ableTI/pws/fotos/eindprod.png

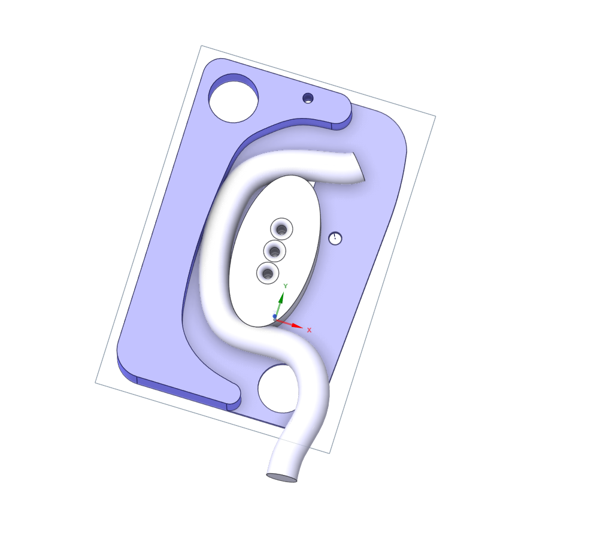
fotos/eindprod.png
