ableTI/pws/fotos/schets_snelheid_ontw.jpg

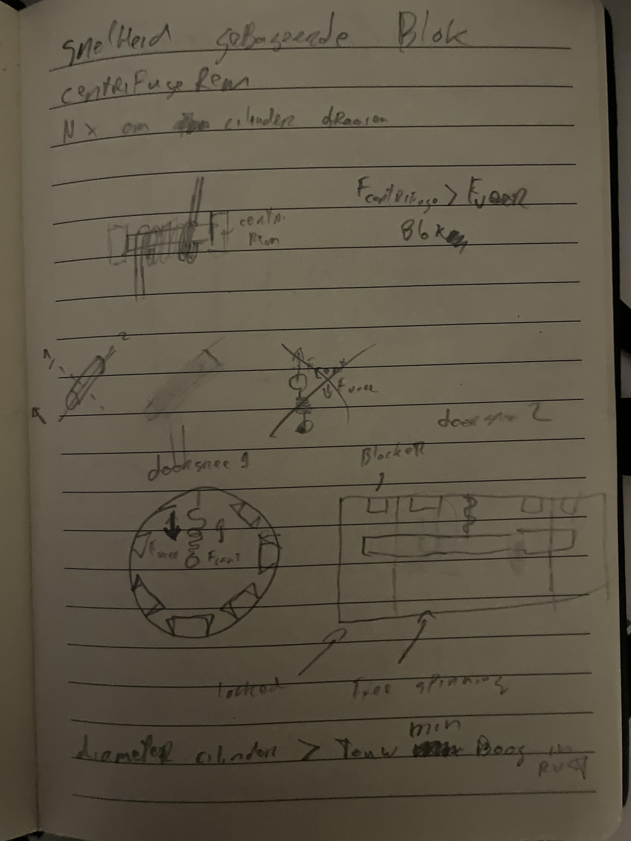
fotos/schets_snelheid_ontw.jpg
