ableTI/pws/fotos/v6.png

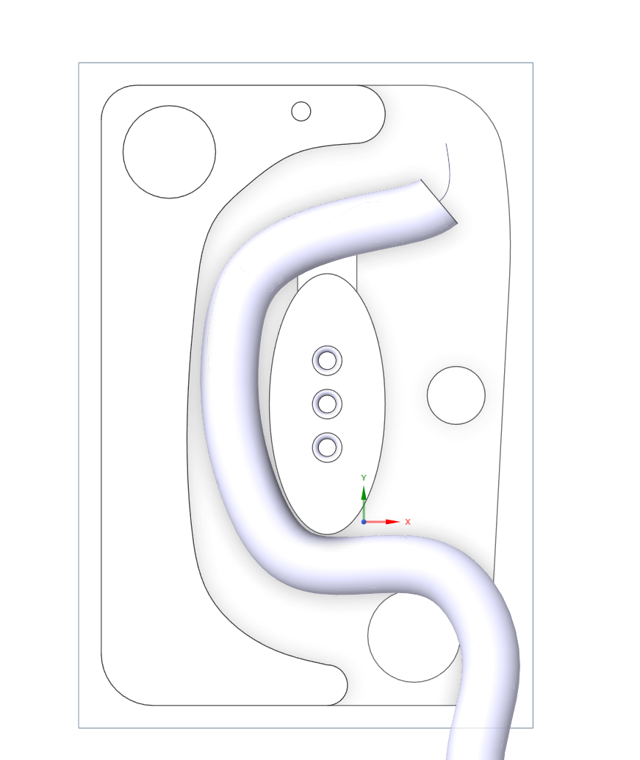
fotos/v6.png
