ableTI/pws/fotos/v6_pl.png

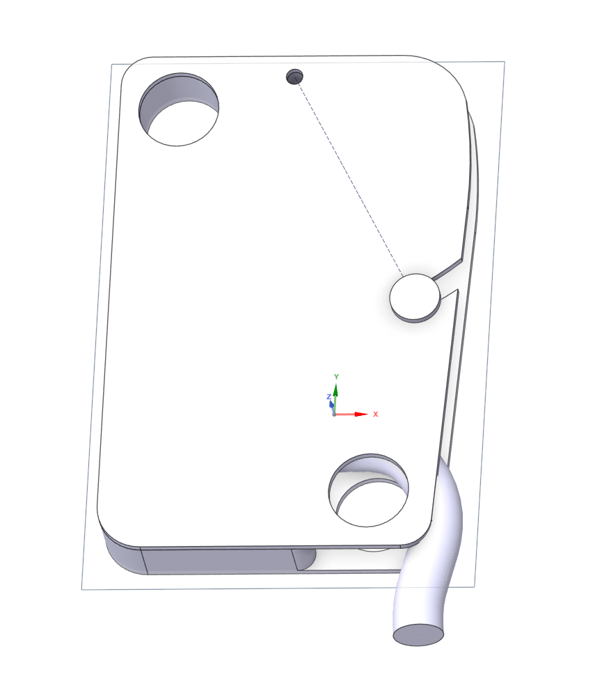
fotos/v6_pl.png
