ableTI/pws/fotos/v8.png

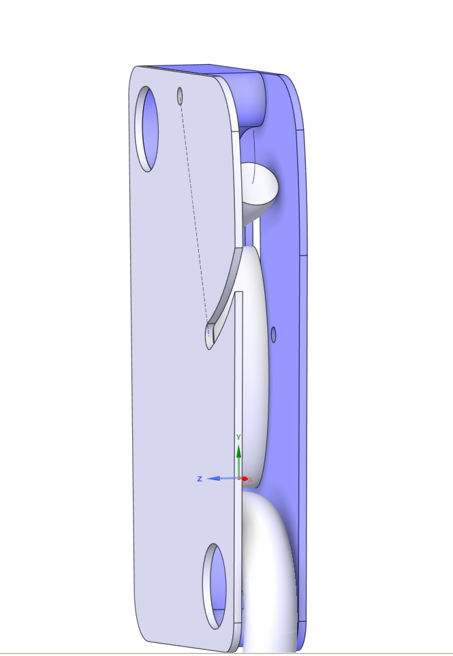
fotos/v8.png
