ableTI/pws/ontwerp/v1/CE3E3V2_cam.3mf

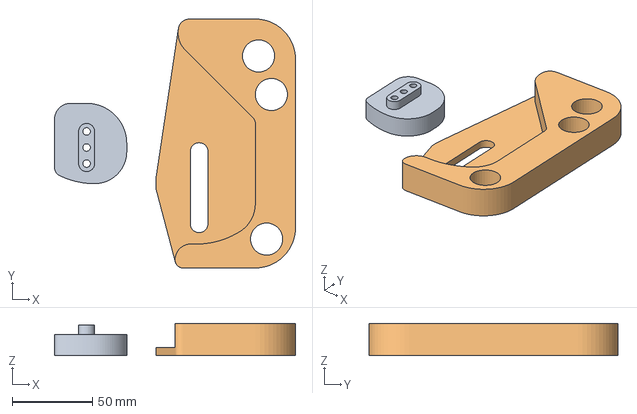
[picture p51: CAD file, 2024-10-30, an earlier design]
ontwerp/v1/CE3E3V2_cam.3mf
150.0 x 155.0 x 20.0 mm
cam.stl
hoofddeel.stl
