ableTI/pws/ontwerp/v2/plaat.stl

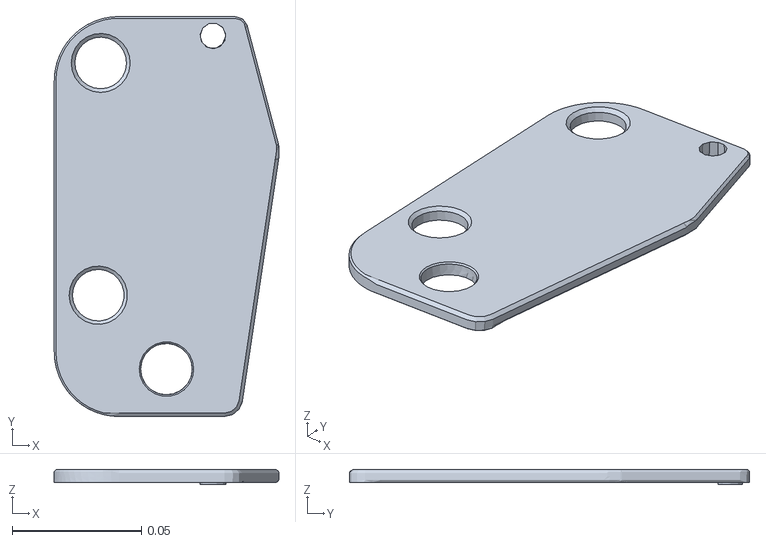
[picture p52: CAD file, 2024-10-30, an earlier design]
ontwerp/v2/plaat.stl
0.087 x 0.155 x 0.00575
