ableTI/pws/ontwerp/v4/cam.stl

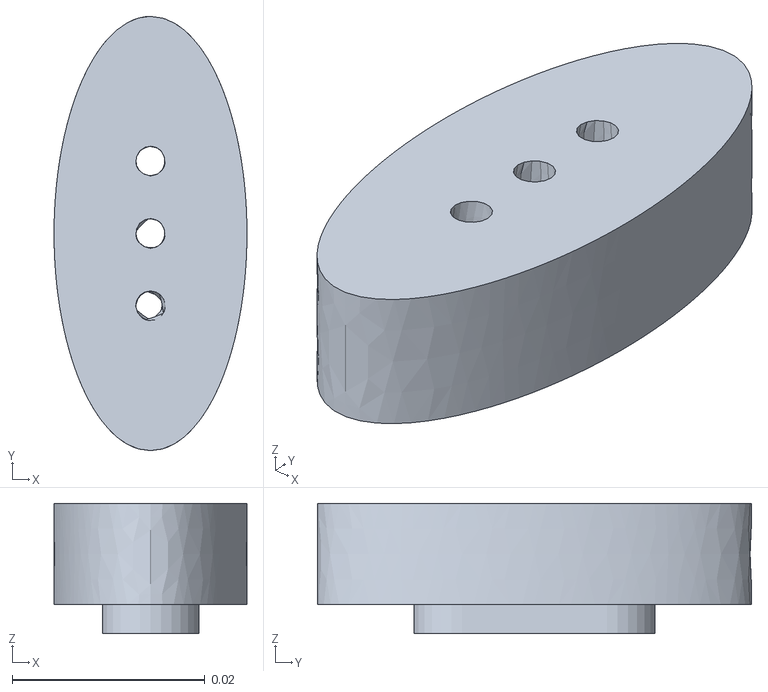
[picture p53: CAD file, 2024-11-01, an earlier design]
ontwerp/v4/cam.stl
0.02 x 0.045 x 0.0135
